DeqingSun/ESP8266-Dash-Button/circuit/img_ assembled.jpg

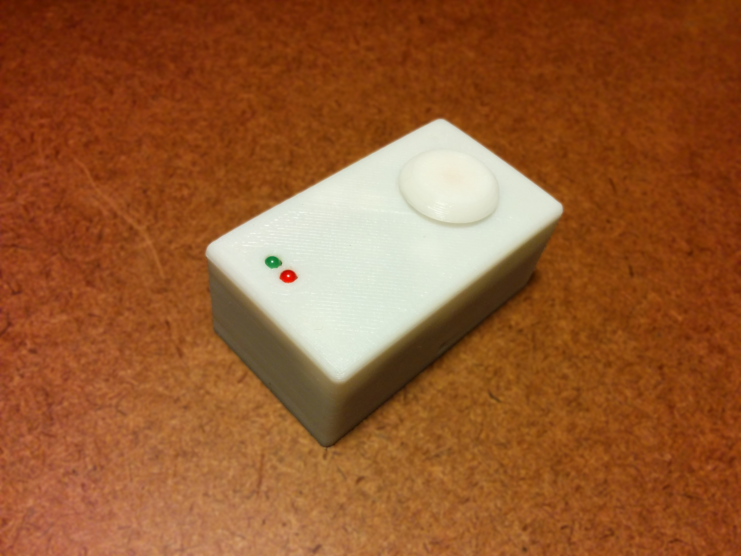
circuit/img_ assembled.jpg
